turtneck/JEB382_ece1895_Duel-It/photos/foil2.png

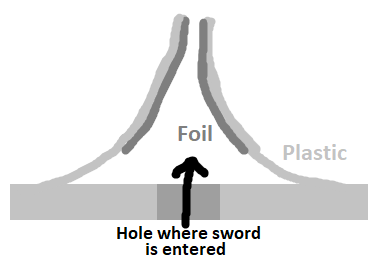
photos/foil2.png
