turtneck/JEB382_ece1895_Duel-It/photos/IMG_6716.jpg

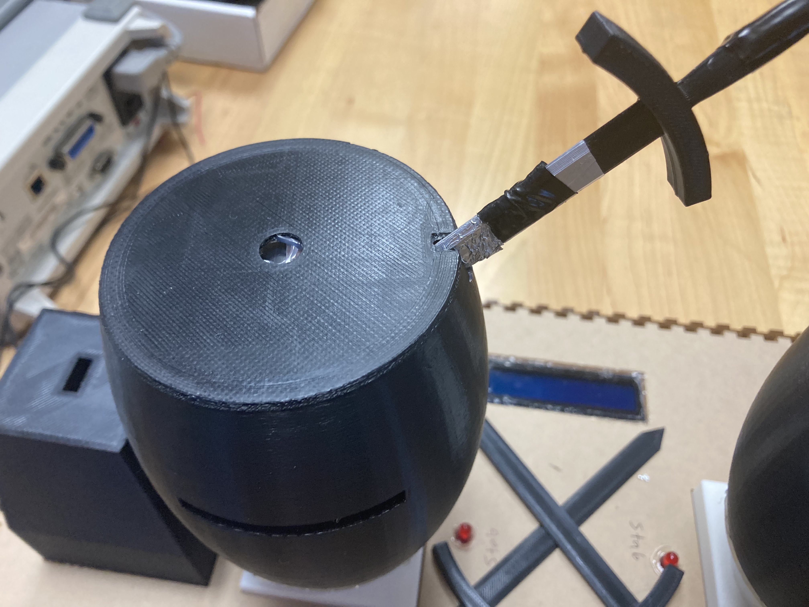
photos/IMG_6716.jpg
