turtneck/JEB382_ece1895_Duel-It/photos/IMG_6717.jpg

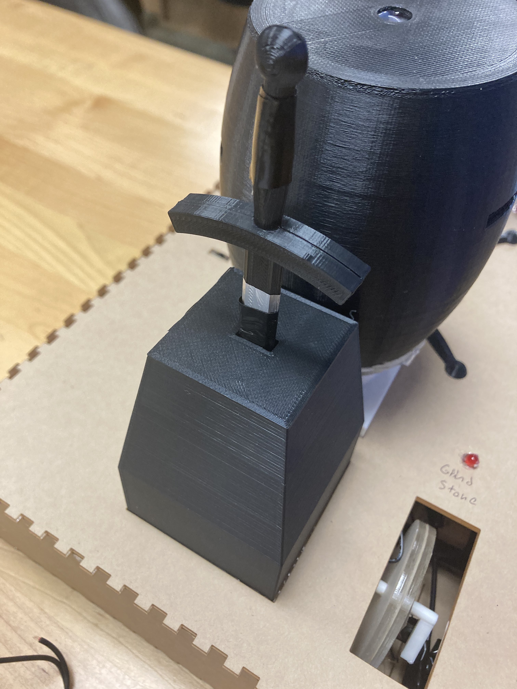
photos/IMG_6717.jpg
