turtneck/JEB382_ece1895_Duel-It/photos/jeb382_1140L12_code.PNG

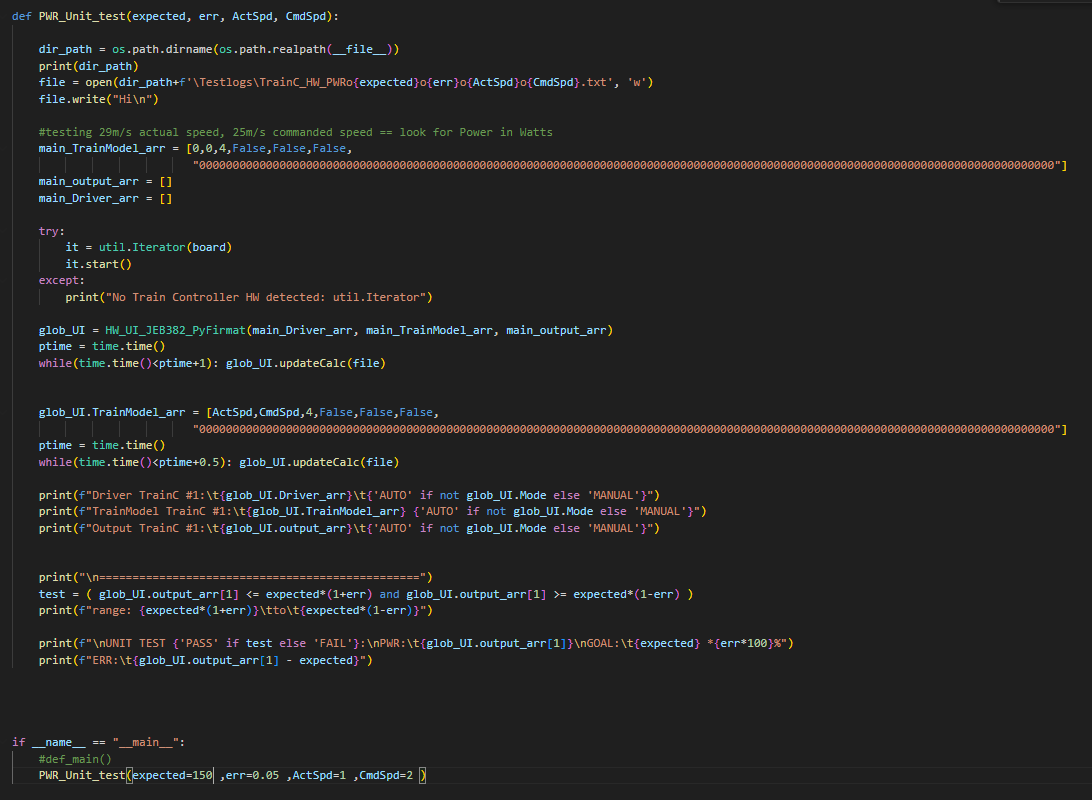
photos/jeb382_1140L12_code.PNG
